nubix-de/opnic/doc/datasheets/MicroUSB-DS.png

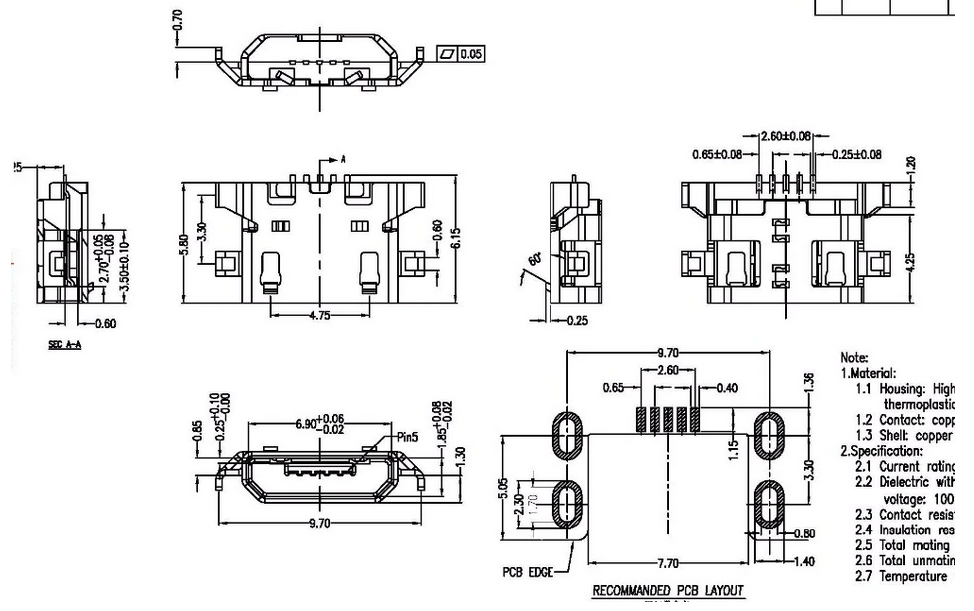
doc/datasheets/MicroUSB-DS.png
