nubix-de/opnic/firmware/cpp/snake/sprites/fullscreen/Flash.png

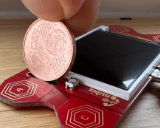
firmware/cpp/snake/sprites/fullscreen/Flash.png
