nubix-de/opnic/firmware/cpp/snake/sprites/fullscreen/SourceCode.png

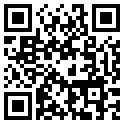
firmware/cpp/snake/sprites/fullscreen/SourceCode.png
