nubix-de/opnic/firmware/micropython/gc9106/apple.py

CONTENT = bytearray(b"\xff\xff\xff\xff\xff\xff\xff\xff\xbb\xb0\xab\x0e\xd1\x8a\x99h\xfc\x8c\xc3\xd1\xb9\x89\xcd\x15\xff\xff\xff\xff\xff\xff\xff\xff\xff\xff\xff\xff\x91\xc9\xd9\x89\xd1(\xf9\x8a\xd1G\xf9\x89\xf9I\xd9(`C\xc0\xe6\xa0\xa5\x98\xc5\xef\xff\xff\xff\xff\xff\xe7]\xf1\x89\xf9(\xd9(\xd9H\xe9H\xe1i\xf9I\xf0\xe7\xe0\xe7\x88\x84\xc8\x85\xa0\x83\xa8\xe6\xff\xff\xff\xff\xe1G\xc8\xe6x\xc5\xa8\xc6\xa1\x07\xf1(\xd0\xc6\xf9i\xf8\xc7\xc0\x84\xb8\x85\x90d\x90\x84\xa0d\xf7\xdf\xf5\x16\xd8\xa5\x90\xa5\x99\x88\x99'\xb1'\xd9\x08\xd1\x06\xfal\xd9G\xe1G\xb9\x05\xa0\xc5p\x02\xa8e\xe9\xca\xf1\xc9\xb0\xc5\x80\xc4\x88\xc5\xc9h\xb1H\xf9\x8a\xe1H\xf9\xeb\xf1\xc9\xf9'\xd0\xe6\xc8\x85\xa8\x85\xa8d\xc0\xe5\xf9\x89\xb0\xc5\xb1&\x98\xe5\xa9&\xf1\x89\xfa\n\xfa,\xfa+\xfaK\xf9\xa9\xf1&\xf0\xe6\xc0\xa6\xb8\x84\xf8\xe6\xf9\xa9\xe1\x05\xb8\xe5\x99F\xd9\x86\xf9\xea\xfal\xf2L\xfa\x8d\xfa\x8d\xfa*\xf9h\xd1\x05\xd0\xc6\xe8\xc6\xf0\xe6\xf9\xea\xf9g\xf9\x87\xf1g\xe9\xa8\xfa*\xfa\xcd\xf2\xad\xfb/\xfb\x0e\xfa\xec\xfa\n\xf9i\xf1(\xf8\xc7\xf9(\xfa\xcd\xf9\xa8\xe1g\xf9\xc8\xfa*\xfa\xcc\xfa\xed\xfbo\xfb\xd1\xfb\xd0\xfb\x0e\xfal\xf9\x89\xf9i\xf9\x07\xf9i\xfc\x12\xfa\n\xfa*\xfa*\xfak\xfa\xcd\xfbp\xfb\xf2\xfcs\xf3\xd1\xfb\xb1\xfa\xee\xfal\xf9\xca\xf9(\xf3\x0f\xff\xff\xfa\x8c\xfal\xfa\xcd\xfb\x0e\xfb\x8f\xfb\xd1\xfcS\xfcS\xfc\xb4\xfcS\xfb/\xfa\xce\xf9\xeb\xf9\xeb\xef\xff\xff\xff\xfc\x12\xfb\x0e\xfbp\xfb\x90\xfc2\xfc\xd4\xfc\xf5\xfd\x16\xfc\xd5\xfcs\xfb\xd1\xfb0\xfa\x8d\xfa\x8d\xff\xff\xff\xff\xff\xff\xfb\xf1\xfb\xf1\xfc2\xfcS\xfc\xf5\xfd6\xfdW\xfdV\xfc\xf5\xfc3\xfb\xf2\xfbp\xff\xff\xff\xff\xff\xff\xff\xff\xf6\xdb\xfc\xb4\xfc\xf5\xfd\x15\xfd\x16\xfdV\xfdw\xfdw\xfd\x16\xfcS\xfc\x94\xff\xbe\xff\xff\xff\xff\xff\xff\xff\xff\xff\xff\xff\xff\xfd\xf8\xfe\x19\xfe\x19\xfd\xf9\xfe\x19\xfd\xf9\xfd\xd9\xfd\xd8\xff\xff\xff\xff\xff\xff\xff\xff")
WIDTH = 16
HEIGHT = 16
